nlbutts/LaserBodyRoll/Mechanical/BUD PN-1312.step

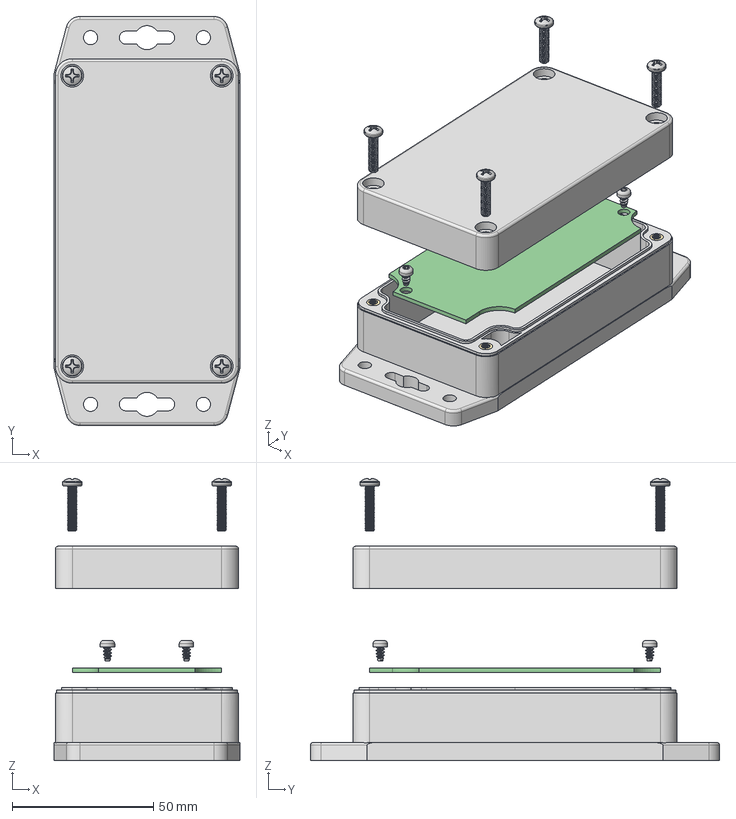
[picture p17: CAD file, 2017-11-27]
Mechanical/BUD PN-1312.step
65.8 x 145.0 x 100.1 mm
Base
Cover
PCB
92000A160 x 4
96817A904 x 2
