nlbutts/LaserBodyRoll/Mechanical/FTSH-105-01-L-D-K.stp

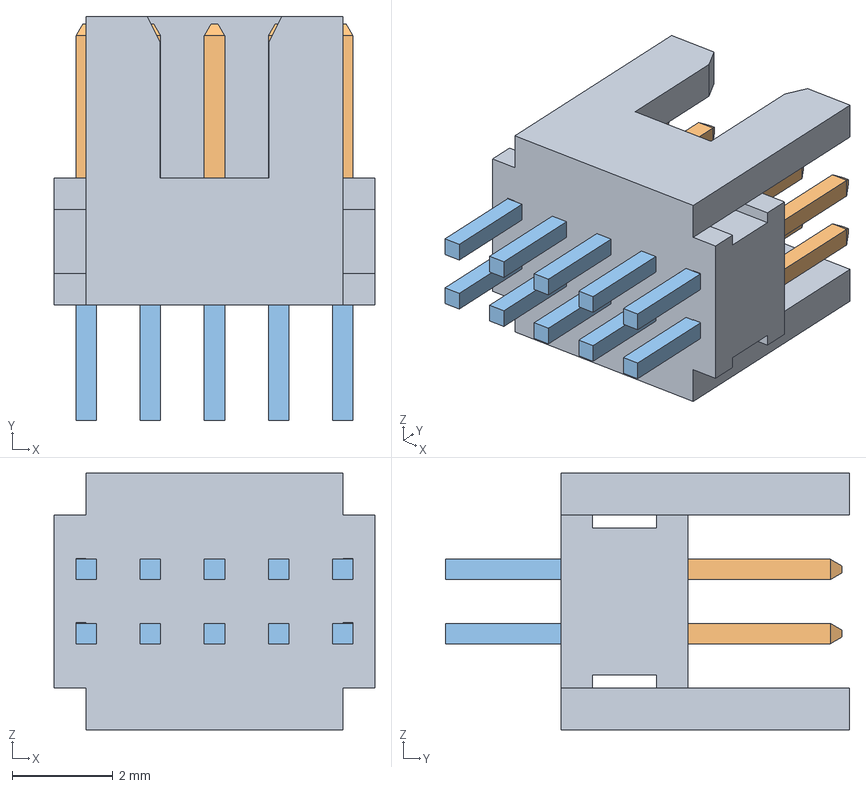
[picture p18: CAD file, 2017-11-22]
Mechanical/FTSH-105-01-L-D-K.stp
6.35 x 8.00 x 5.08 mm
_FTSH-105-01-L-D-K_body
_FTSH-105-01-L-D-K_pins1
_FTSH-105-01-L-D-K_pins2
