nlbutts/LaserBodyRoll/Hardware/simulation/opamp_voltage_follower.asc

R1: res; 44.2k
R2: res; 24.3k
U1: AD823
V1: voltage; 5
V2: voltage; SINE(0 3.3 1)
Named nets: 0
.tran 0.5
