nlbutts/LaserBodyRoll/Hardware/simulation/output_protection.asc

Q1: npn
R1: res; 24.3k
R2: res; 330
R3: res; 24.3k
R4: res; 100k
V1: voltage; PULSE(0 3.3 0.1 0 20e-6 .1 .2 1)
V2: voltage; 12
Named nets: 0
.tran 0.2
