nlbutts/LaserBodyRoll/Hardware/simulation/input_protection.asc

Q1: npn
R1: res; 23.2k
R2: res; 23.2k
R3: res; 75k
V1: voltage; PULSE(0 12 0.1 0 20e-6 .1 .2 1)
V2: voltage; 5
Named nets: 0
