nlbutts/LaserBodyRoll/Hardware/simulation/esd_analog_input.asc

D1: zener; 1N750
D2: zener; 1N750
R1: res; 10MEG
R2: res; 23.2k
V1: voltage; PULSE(1 20000 0 0 0 20e-6 .2 1)
V2: voltage; 5
Named nets: 0
.tran 50e-6
