nlbutts/LaserBodyRoll/Hardware/simulation/esd_analog_out.asc

C1: cap; 1n
D2: zener; 1N750
R2: res; 23.2k
U1: LT1001
V1: voltage; PULSE(1 20000 10e-6 0 0 20e-6 .2 1)
V2: voltage; 1
Named nets: 0
.tran 50e-6
